sTeeLM/Dimmable_Microscope_Illuminator/src/led.h

#ifndef __DMI_LED_H__
#define __DMI_LED_H__

#include <stdint.h>

typedef struct _led_cfg_t
{
  uint16_t brightness; /* 0 ~ 1000*/
  uint16_t color;      /* 0 ~ 1000*/
}led_cfg_t;

extern led_cfg_t led_cfg;

void led_factory_reset(void);
void led_initialize(void);

void led_inc_color(bit fast);
void led_dec_color(bit fast);
void led_inc_brightness(bit fast);
void led_dec_brightness(bit fast);
uint16_t led_get_brightness(void);
uint16_t led_get_color(void);

void led_power_off(void);
void led_power_on(void);

#endif
