sTeeLM/Dimmable_Microscope_Illuminator/src/task.c

#include <stdio.h>
#include <string.h>
#include <stdint.h>

#include "clock.h"
#include "task.h"
#include "debug.h"
#include "sm.h"

/* hardware*/
#include "button.h"

const char * code task_names[] =
{
  "EV_KEY_SCAN",  
  "EV_250MS",
  "EV_1S",
  "EV_KEY_DOWN",
  "EV_KEY_PRESS",
  "EV_KEY_LPRESS",
  "EV_KEY_UP",  
  "EV_KEY_CC",
  "EV_KEY_F_CC",  
  "EV_KEY_C",
  "EV_KEY_F_C",  
  "EV_TIMEO", 
};

static void null_proc(enum task_events ev)
{
  sm_run(ev);
}


static const TASK_PROC task_procs[EV_CNT] = 
{
  /* EV_SCAN_KEY */
  button_scan_proc, 
  /* EV_250MS*/
  clock_time_proc,
  /* EV_1S*/
  clock_time_proc,
  /* EV_KEY_XX */
  button_proc,
  button_proc,
  button_proc,
  button_proc,
  button_proc,
  button_proc,
  button_proc,
  button_proc,
  null_proc, 
};


uint16_t ev_bits0;
uint16_t ev_bits1;

void task_initialize (void)
{
  CDBG("task_initialize\n");
  ev_bits0 = 0;
  ev_bits1 = 0;
}

void task_run(void)
{
  uint8_t c;
  for(c = 0; c < EV_CNT; c++) {
    if(task_test(c)) {
      task_clr(c);
      task_procs[c](c);
    }
  }
}

void task_dump(void)
{
  uint8_t i;
  for (i = 0 ; i < EV_CNT; i ++) {
    CDBG("[%02bd][%s] %c\n", i, task_names[i], task_test(i) ? '1' : '0');
  }
}
